tero/rae-dux/output/routed_pcbs/board-back.png

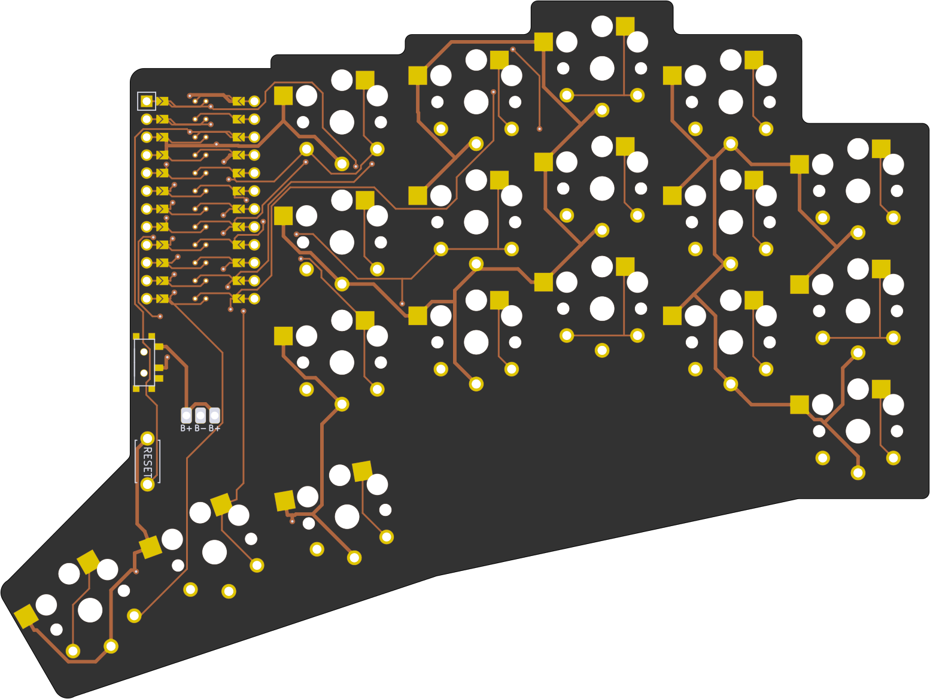
output/routed_pcbs/board-back.png
