tero/rae-dux/output/routed_pcbs/board-front.png

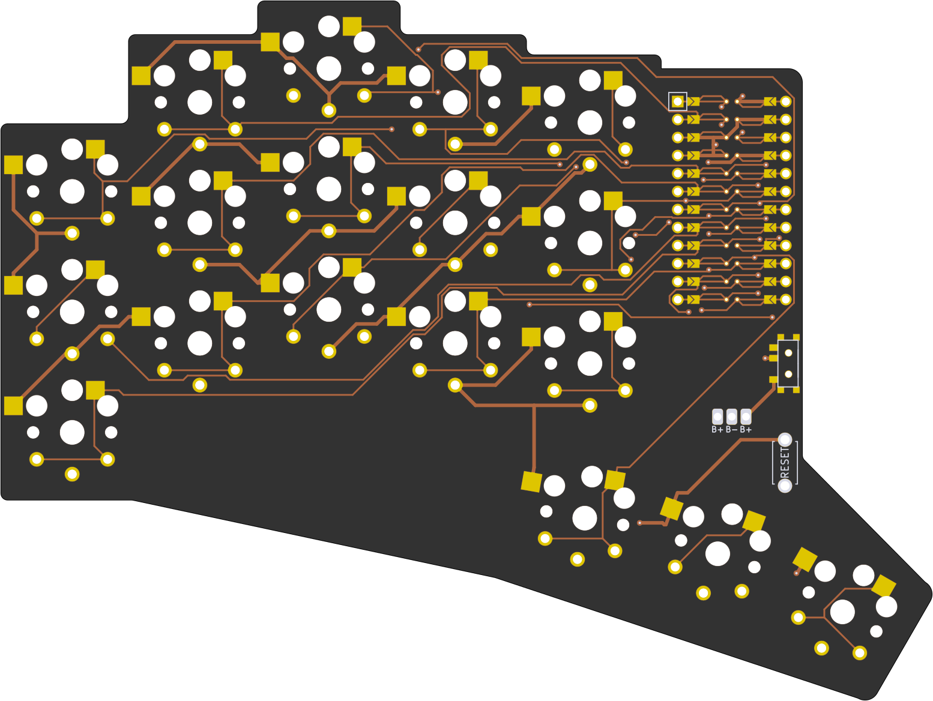
output/routed_pcbs/board-front.png
